davek184/EC23U/Docs/23U Internals/5 - esSN8OQ.jpg

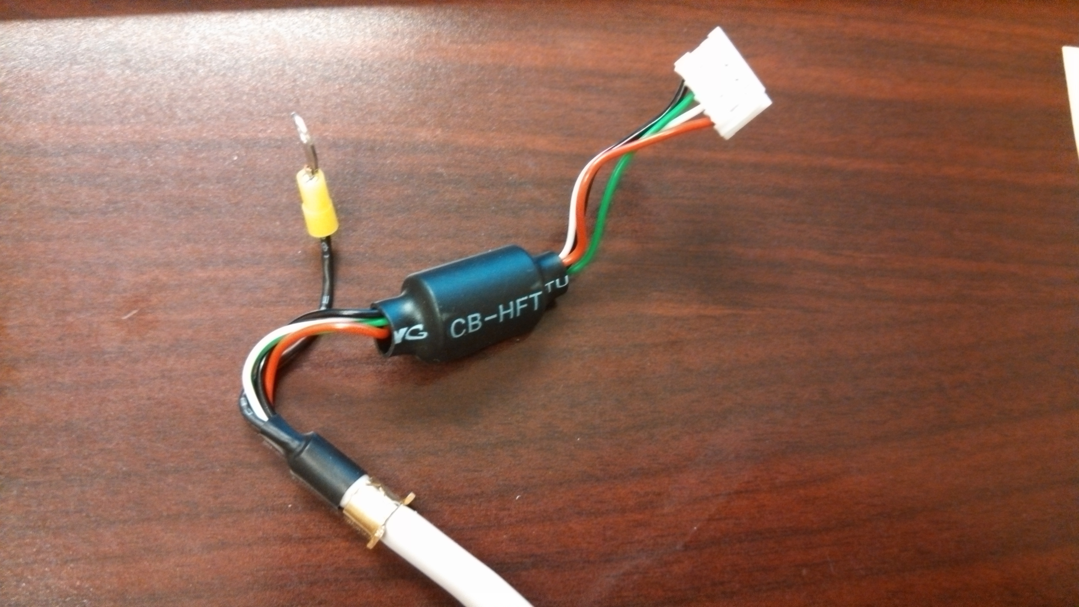
Docs/23U Internals/5 - esSN8OQ.jpg
