davek184/EC23U/Docs/23U Internals/6 - TECfzAd.jpg

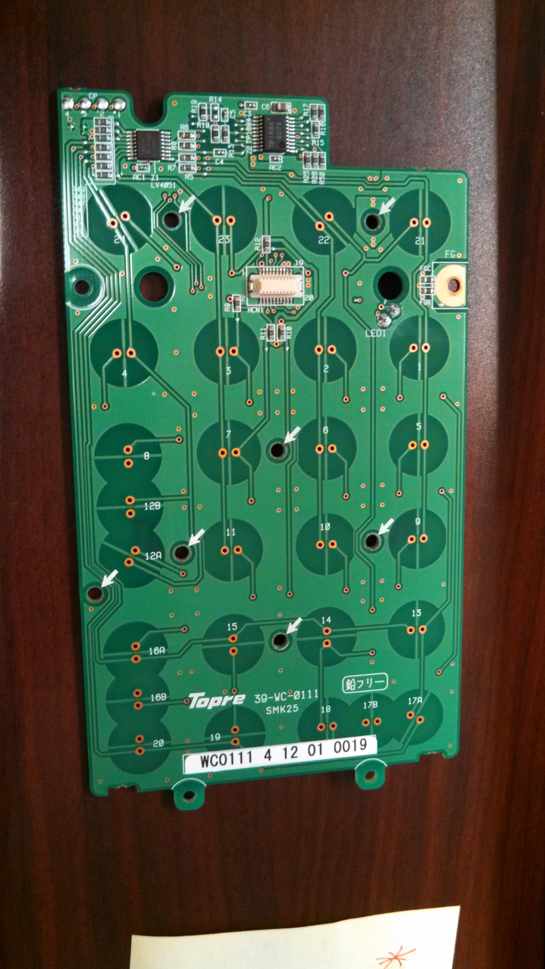
Docs/23U Internals/6 - TECfzAd.jpg
